omarwaelppmm-a11y/Incubator/Real life photos/photo_2026-06-25_06-56-48.jpg

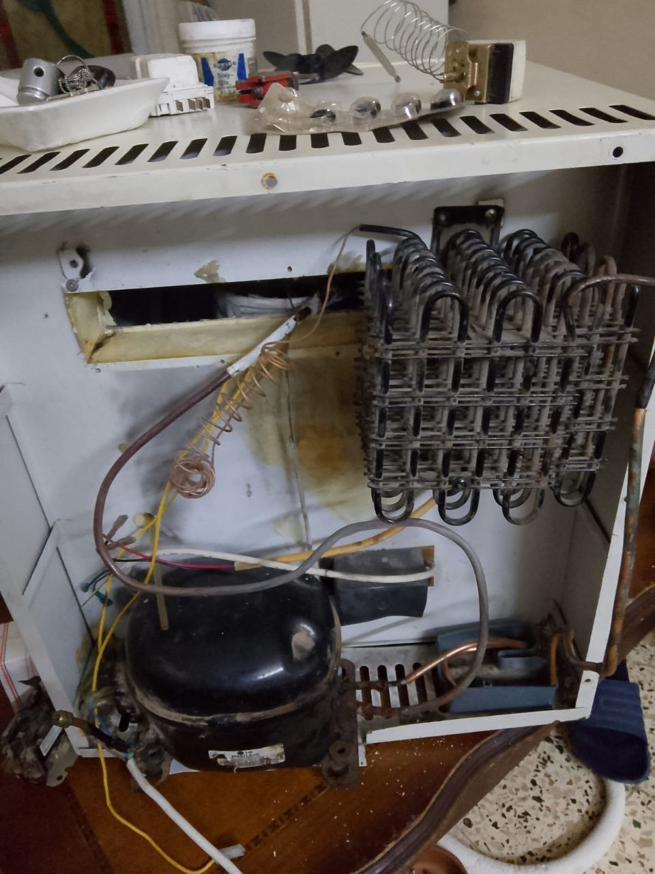
Real life photos/photo_2026-06-25_06-56-48.jpg
