omarwaelppmm-a11y/Incubator/Real life photos/Screenshot 2026-08-19 174736.png

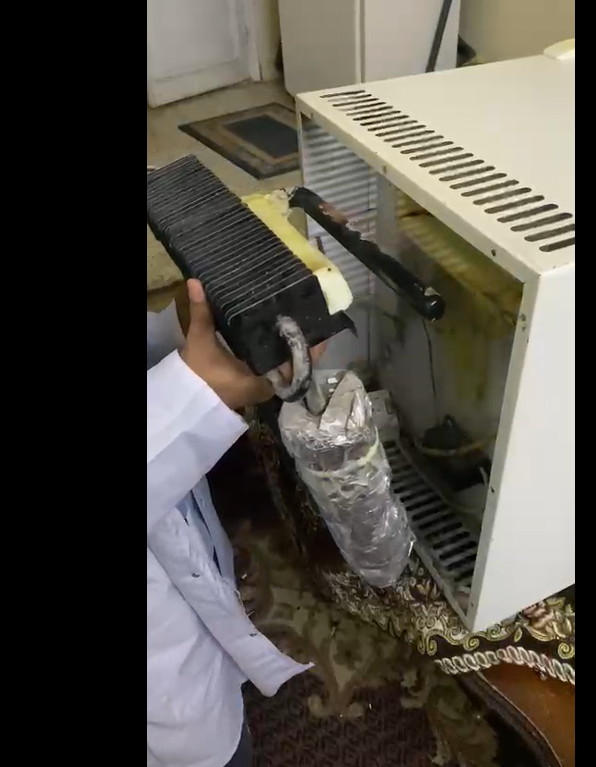
Real life photos/Screenshot 2026-08-19 174736.png
