omarwaelppmm-a11y/Incubator/Real life photos/Screenshot 2026-08-19 174811.png

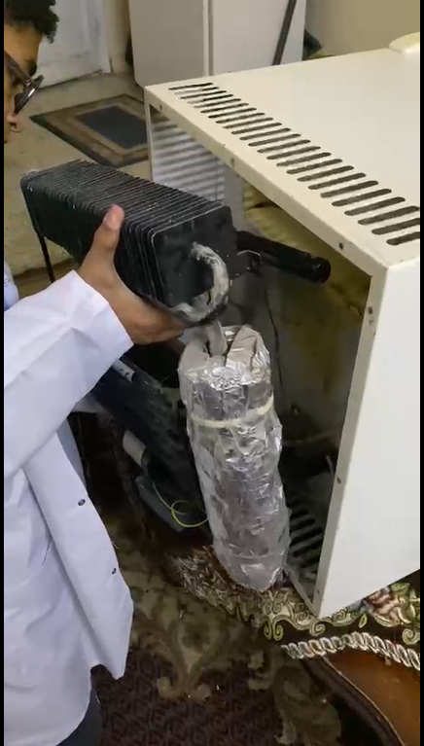
Real life photos/Screenshot 2026-08-19 174811.png
